Shamanta14/HSHL-Prototyping-E2-E4/CAD_Designs /CAD_Designs/Ball Bearing Height Extension.png

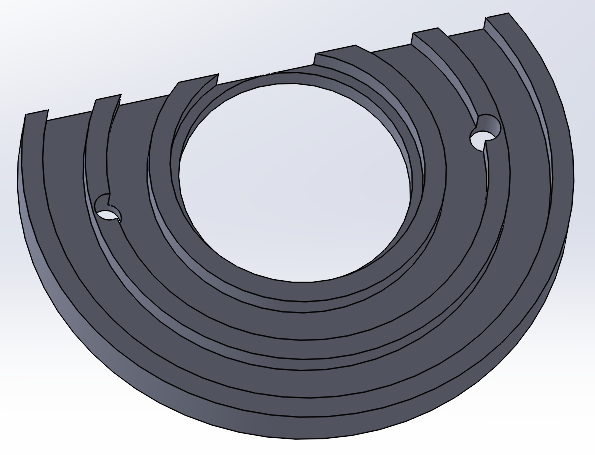
CAD_Designs /CAD_Designs/Ball Bearing Height Extension.png
