Shamanta14/HSHL-Prototyping-E2-E4/CAD_Designs /CAD_Designs/Bambu_Studio_Time_Taking.png

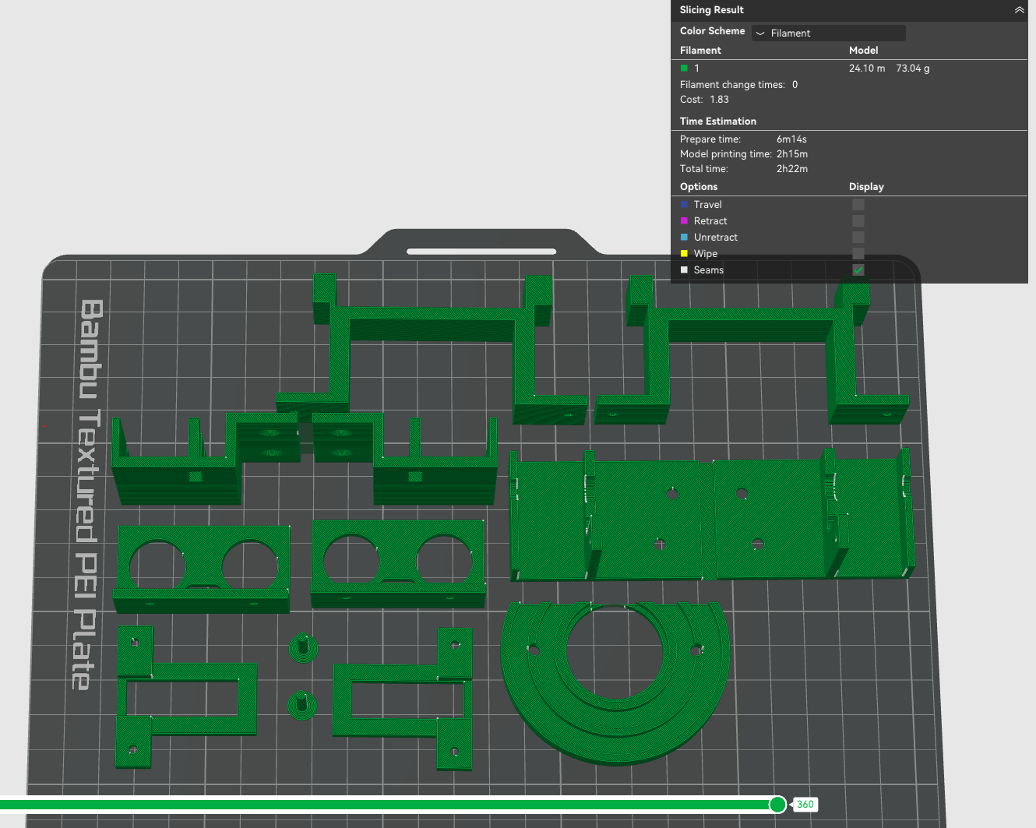
CAD_Designs /CAD_Designs/Bambu_Studio_Time_Taking.png
