Shamanta14/HSHL-Prototyping-E2-E4/CAD_Designs /CAD_Designs/GearMotor_Holder/Top_Part_First_Angle.png

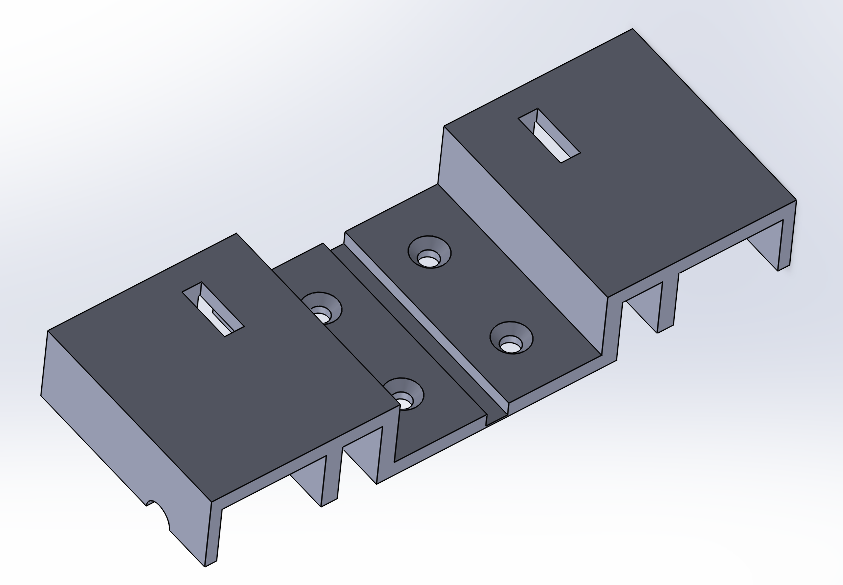
CAD_Designs /CAD_Designs/GearMotor_Holder/Top_Part_First_Angle.png
