Shamanta14/HSHL-Prototyping-E2-E4/Main_Robot_Project/Motor Driver/Tinkercad Motordriver.png

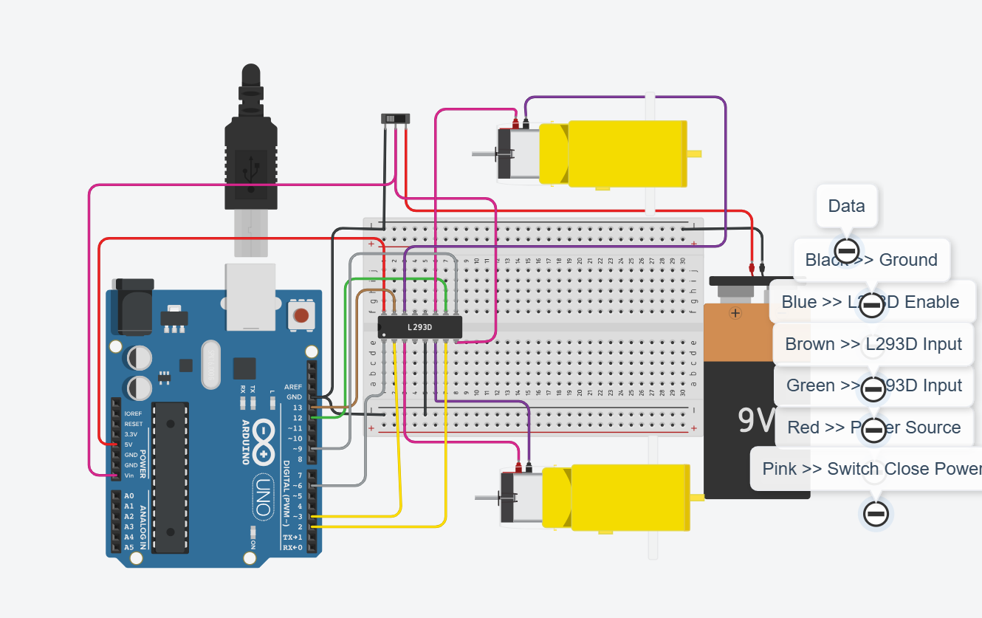
Main_Robot_Project/Motor Driver/Tinkercad Motordriver.png
