Shamanta14/HSHL-Prototyping-E2-E4/System&UML_diagrams/Package Diagram.png

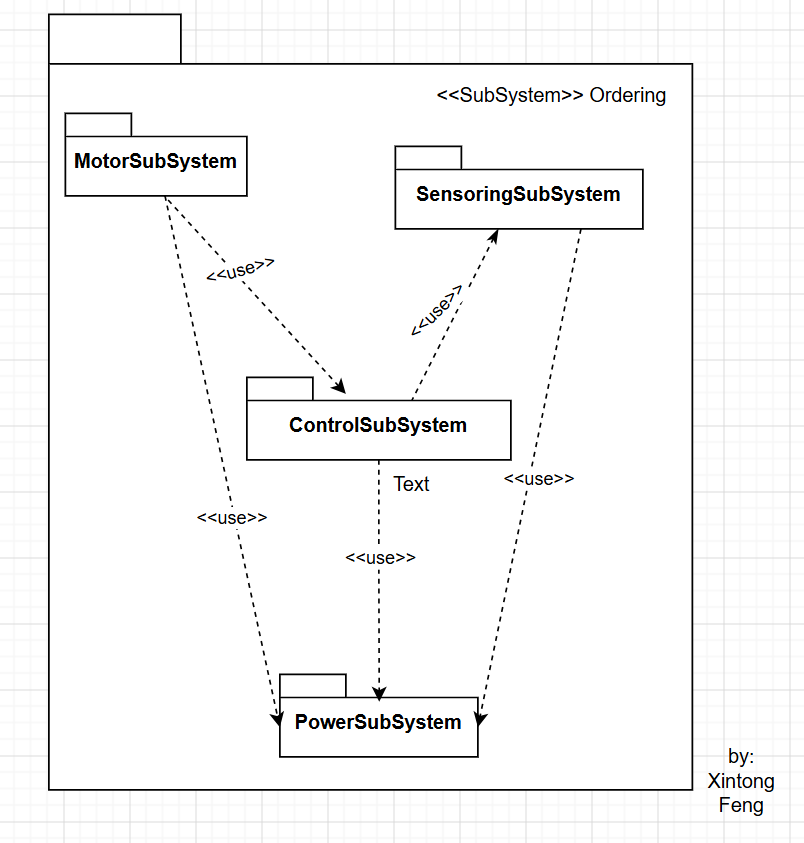
System&UML_diagrams/Package Diagram.png
