Shamanta14/HSHL-Prototyping-E2-E4/System&UML_diagrams/SMD_diagram.drawio.png

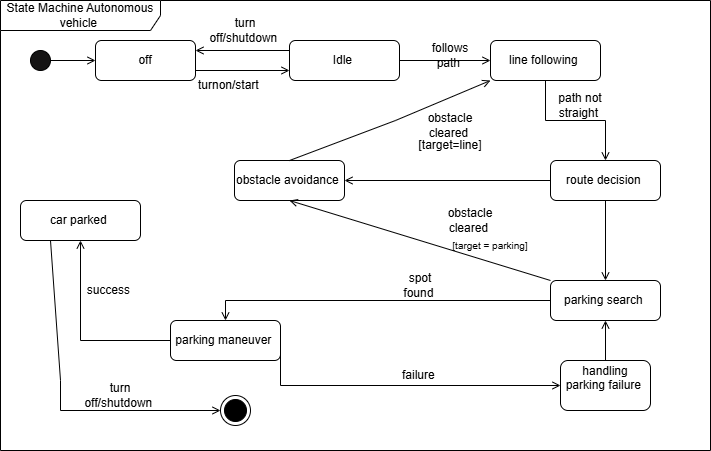
System&UML_diagrams/SMD_diagram.drawio.png
