Shamanta14/HSHL-Prototyping-E2-E4/System&UML_diagrams/Updated Diagram/Activity_diagram2F.drawio.png

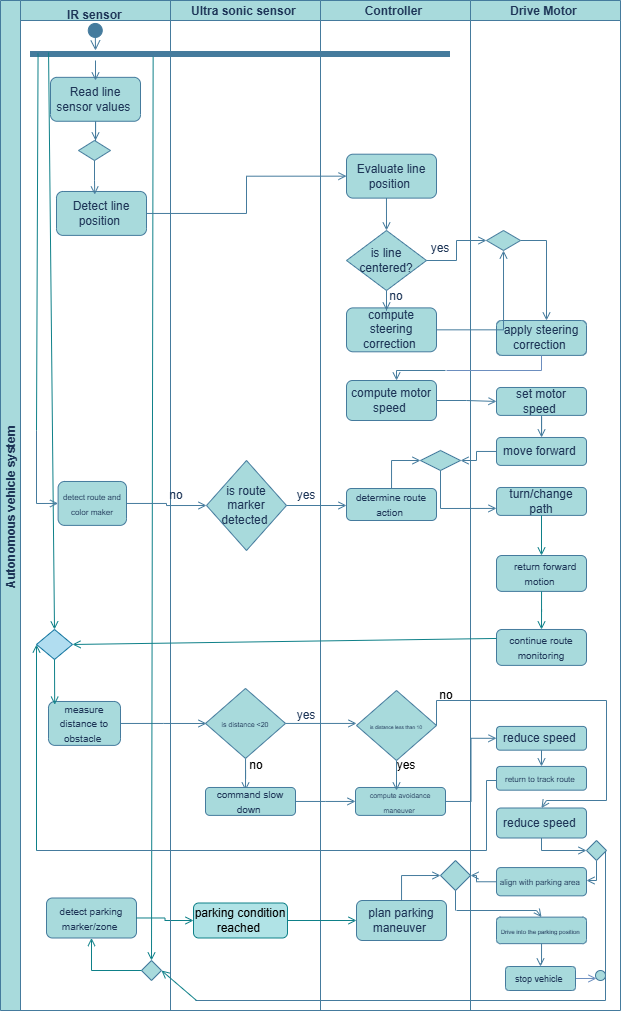
System&UML_diagrams/Updated Diagram/Activity_diagram2F.drawio.png
