Shamanta14/HSHL-Prototyping-E2-E4/System&UML_diagrams/Updated Diagram/Requirements Diagram final.png

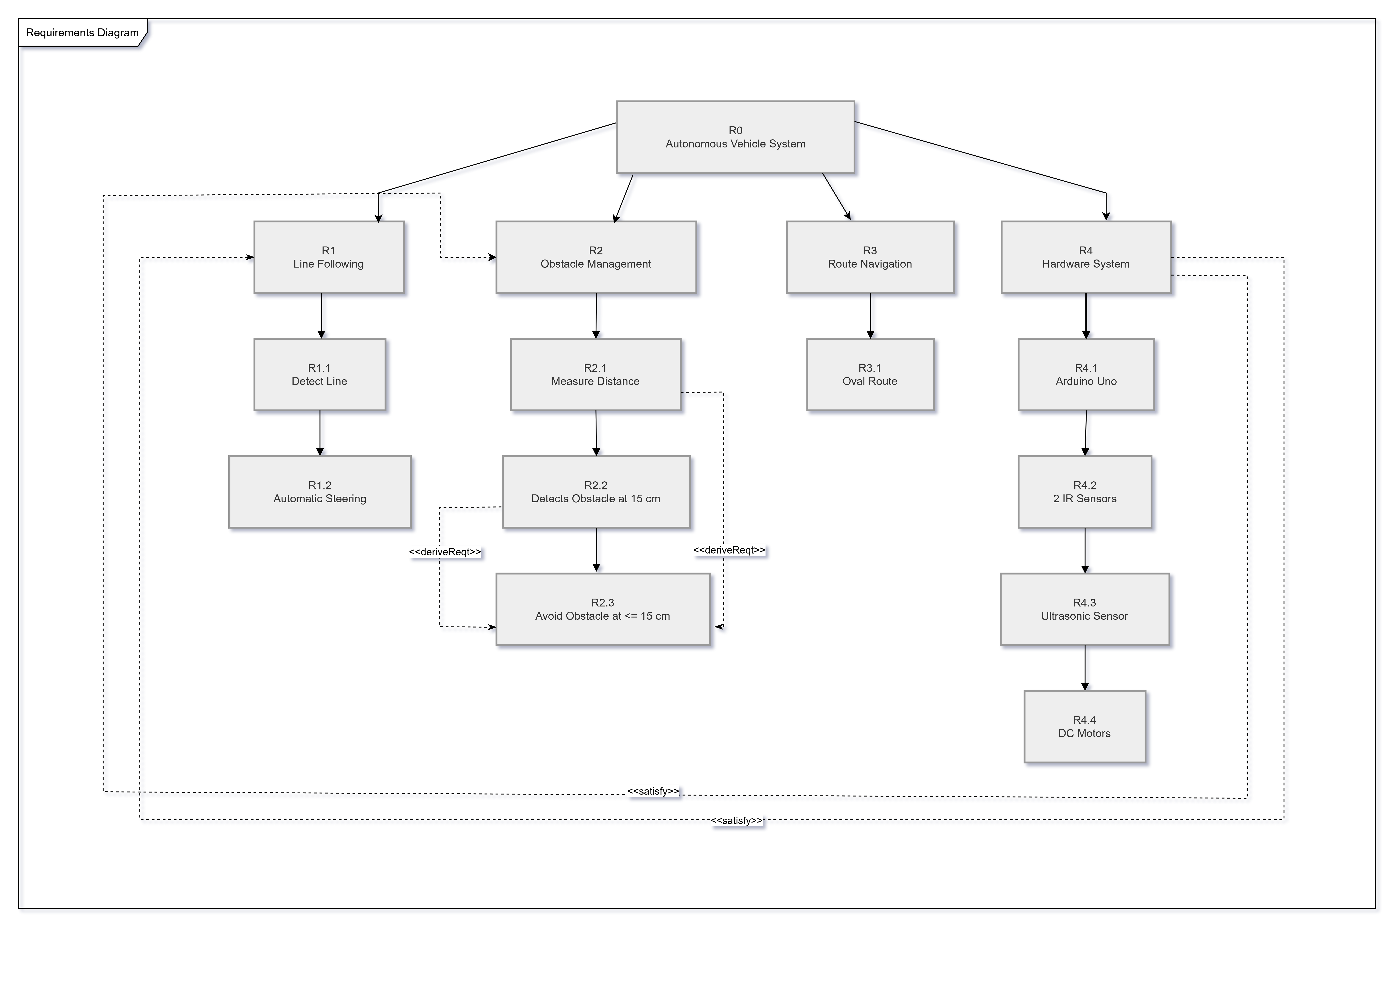
System&UML_diagrams/Updated Diagram/Requirements Diagram final.png
