Shamanta14/HSHL-Prototyping-E2-E4/System&UML_diagrams/Updated Diagram/State Machine Diagram.png

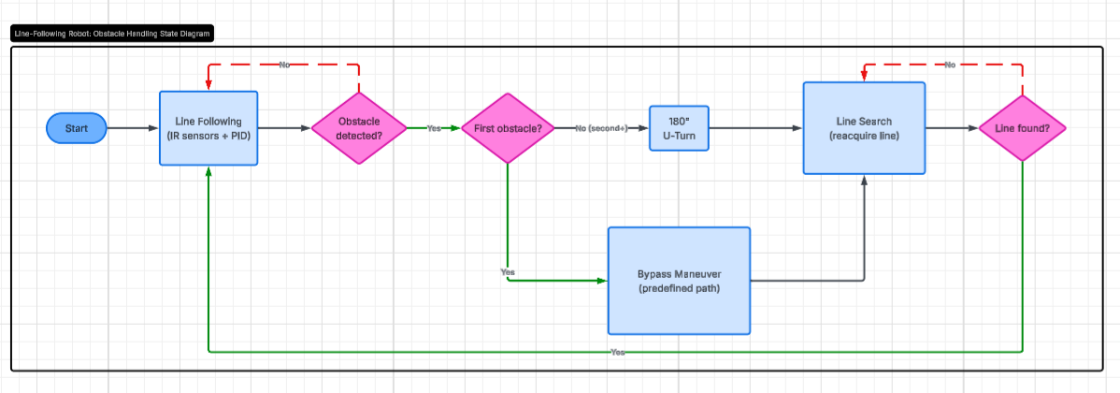
System&UML_diagrams/Updated Diagram/State Machine Diagram.png
