Shamanta14/HSHL-Prototyping-E2-E4/System&UML_diagrams/Use case (Xintong Feng).png

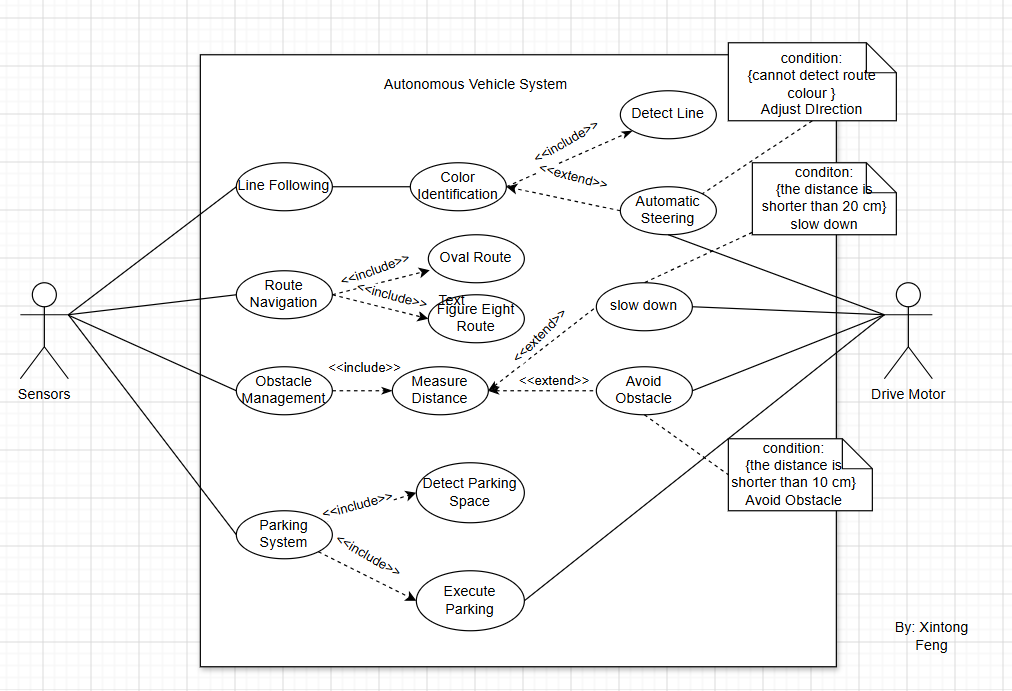
System&UML_diagrams/Use case (Xintong Feng).png
