Shamanta14/HSHL-Prototyping-E2-E4/CAD_Designs /CAD_Designs/Real World Assembly/Back_View.jpeg

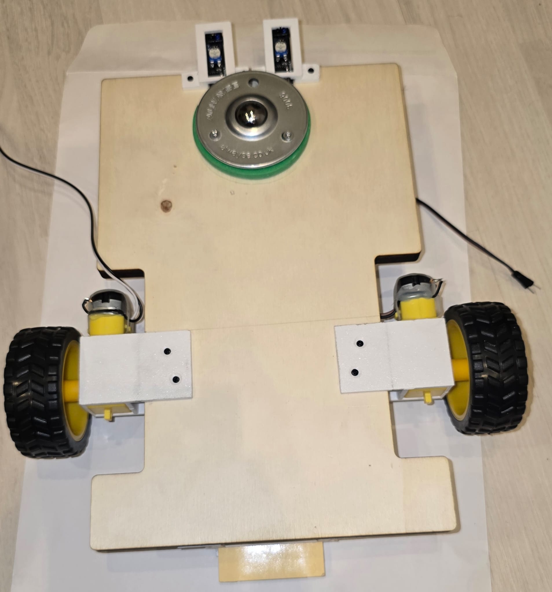
CAD_Designs /CAD_Designs/Real World Assembly/Back_View.jpeg
