Shamanta14/HSHL-Prototyping-E2-E4/Main_Robot_Project/Assembled Parts/Final Assembled Robot.jpeg

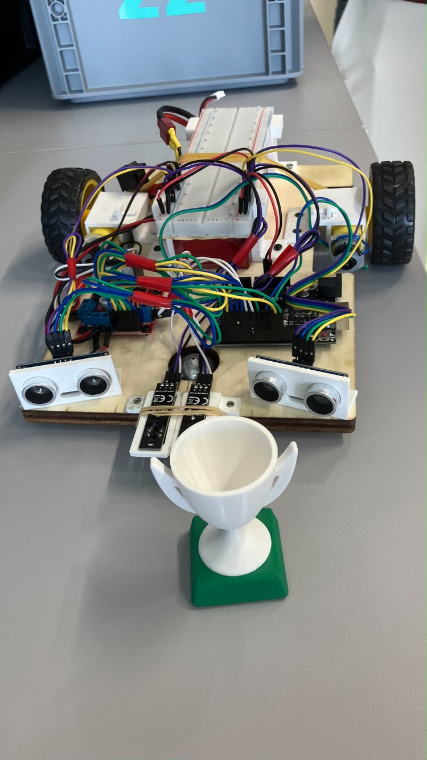
Main_Robot_Project/Assembled Parts/Final Assembled Robot.jpeg
