Shamanta14/HSHL-Prototyping-E2-E4/Main_Robot_Project/Tinkercad_circuitwiring/Initial TinkerCad_Diagram.png

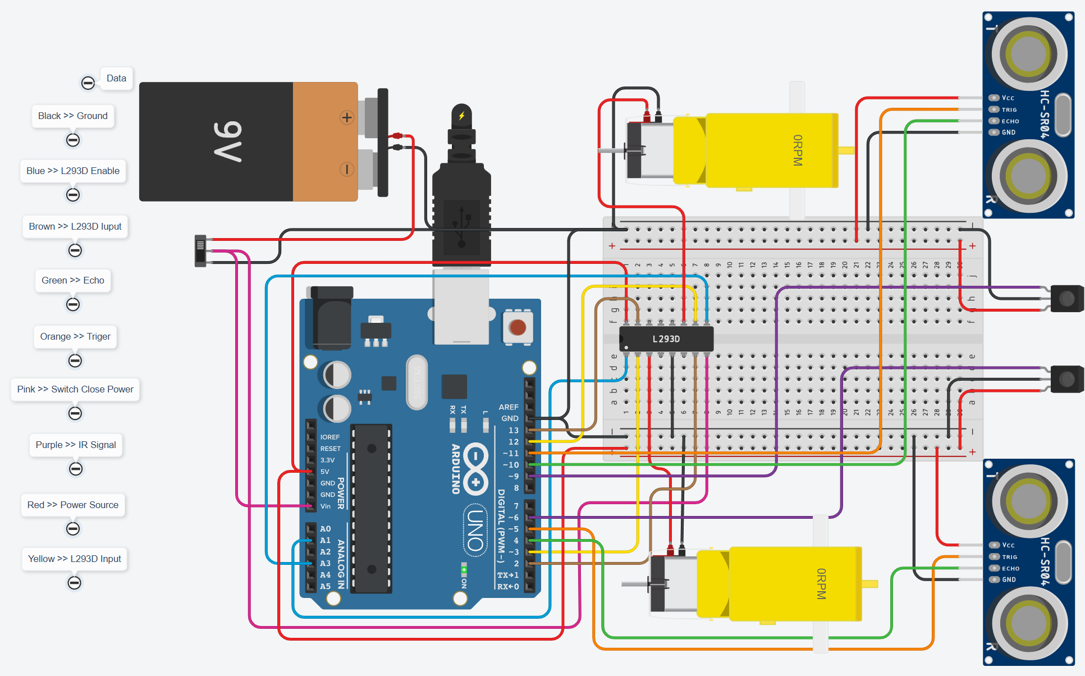
Main_Robot_Project/Tinkercad_circuitwiring/Initial TinkerCad_Diagram.png
