Shamanta14/HSHL-Prototyping-E2-E4/Sensors_Testing/GearMotor/tinkercad_wiring.png

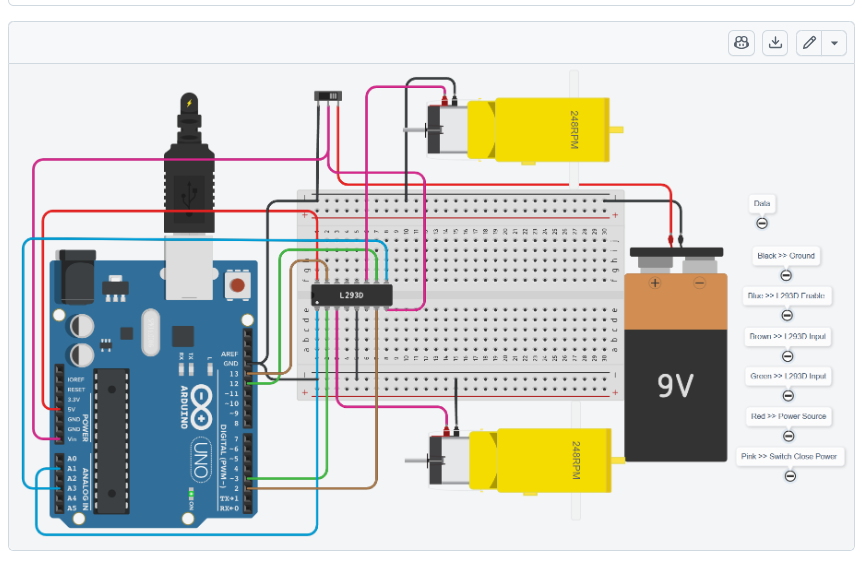
Sensors_Testing/GearMotor/tinkercad_wiring.png
