Shamanta14/HSHL-Prototyping-E2-E4/Sensors_Testing/IR_ Sensor/Initial TinkerCad_Diagram.png

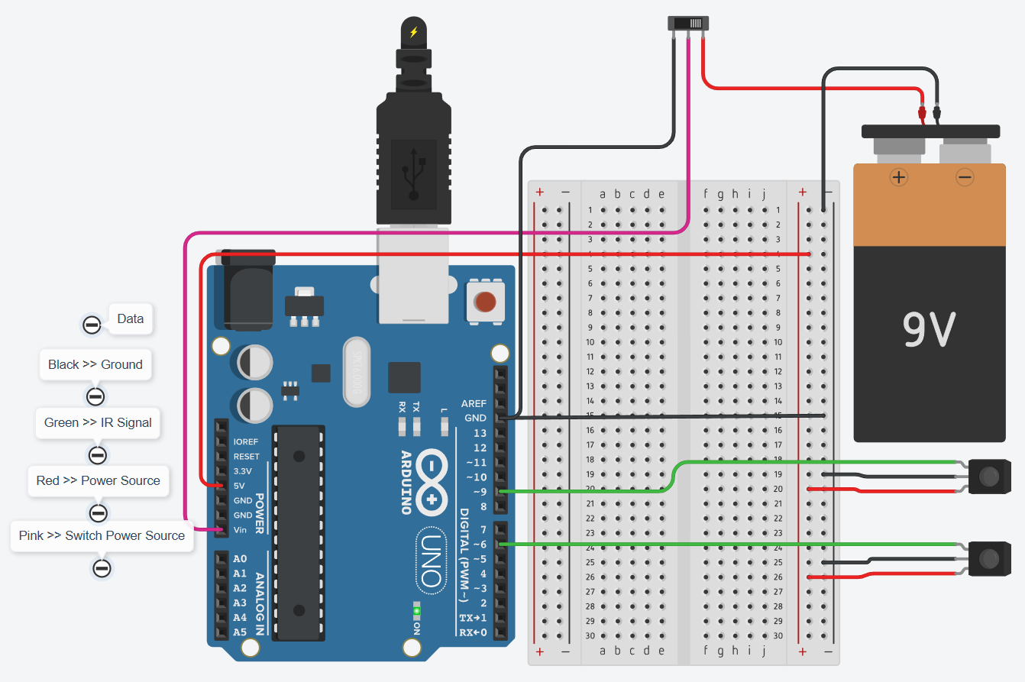
Sensors_Testing/IR_ Sensor/Initial TinkerCad_Diagram.png
