Shamanta14/HSHL-Prototyping-E2-E4/Sensors_Testing/IR_ Sensor/Modified Tinkercad Diagram.jpeg

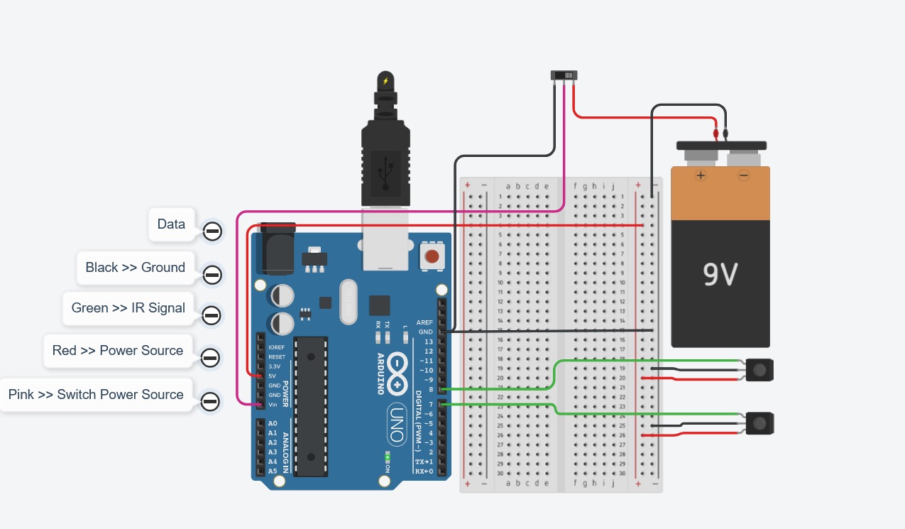
Sensors_Testing/IR_ Sensor/Modified Tinkercad Diagram.jpeg
