Shamanta14/HSHL-Prototyping-E2-E4/Sensors_Testing/Ultra_Sonic_Sensor/TinkerCad_Diagram.png

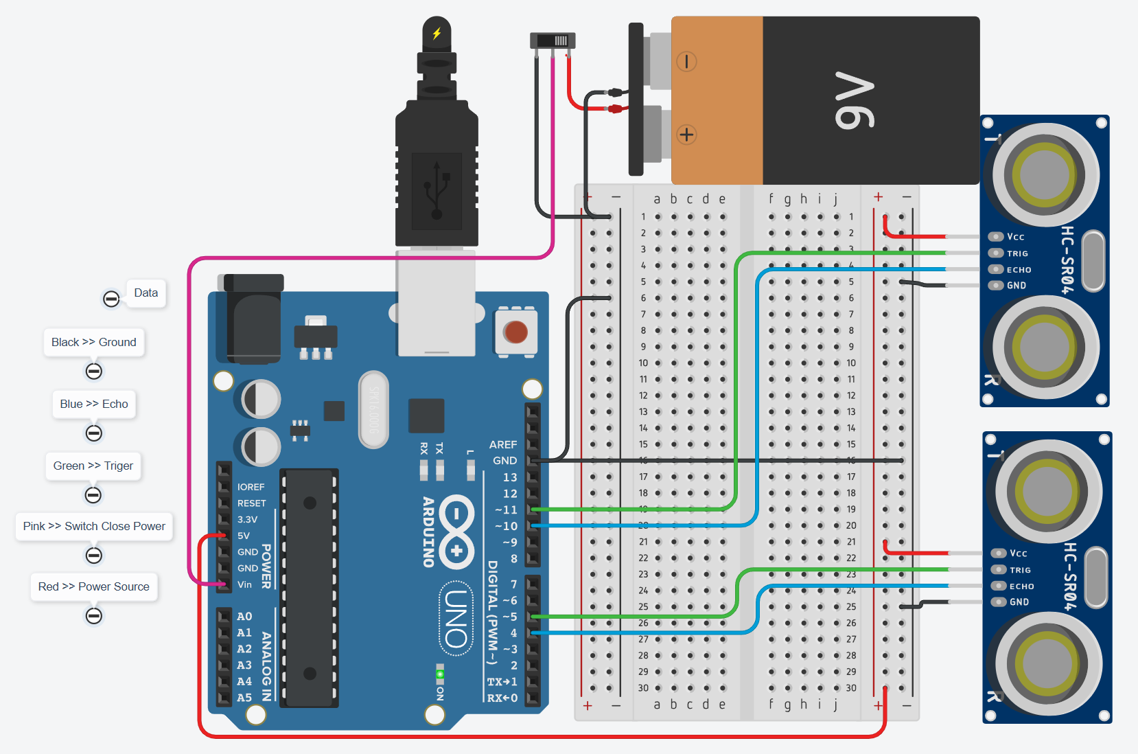
Sensors_Testing/Ultra_Sonic_Sensor/TinkerCad_Diagram.png
