Shamanta14/HSHL-Prototyping-E2-E4/Main_Robot_Project/Pin_Connections.h

///////////////////////////////////////////////////////
            Motor Driver Pin Connections
///////////////////////////////////////////////////////
=======================================================
Motor Driver Pins           |          Arduino Uno Pins
=======================================================
Power 1(5V)                                     5V

Power 2(12v)                               From Switch
-------------------------------------------------------
                  Left Gear Motor
-------------------------------------------------------
Enable 1 & 2                                6

Input 1                                     2

Input 2                                     3

Output 1                                 To Positive terminal of the Right Gear Motor 
Output 2                                 To Negative terminal of the Right Gear Motor 
-------------------------------------------------------
                  Right Gear Motor
-------------------------------------------------------
Enable 3 & 4                                5

Input 3                                     12

Input 4                                     13

Output 3                                 To Positive terminal of the Left Gear Motor 
Output 4                                 To Negative terminal of the Left Gear Motor 
=======================================================


///////////////////////////////////////////////////////
          Ultra Sonic Sensor Pin Connections
///////////////////////////////////////////////////////
=======================================================
Ultra Sonic Sensor Pins    |           Arduino Uno Pins
=======================================================
-------------------------------------------------------
                   First Ultra Sonic
-------------------------------------------------------
Trigger                                    11

Echo                                       10
-------------------------------------------------------
                  Second Ultra Sonic
-------------------------------------------------------
Trigger                                    9

Echo                                       4
=======================================================


///////////////////////////////////////////////////////
            IR Sensor Pin Connections
///////////////////////////////////////////////////////
=======================================================
IR Sensor Pins            |            Arduino Uno Pins
=======================================================
IR sensor 1                                 8

IR sensor 2                                 7
=======================================================
